mancusoa74/Walvola/Software/Walvola/telegram.cpp

//#include "telegram.h"

//TelegramBOT tgram_bot(TGRAM_BOTtoken, TGRAM_BOTname, TGRAM_BOTusername);
//String tgram_listener[TGRAM_LISTENER_SIZE] =  { "YOUR TELEGRAM BOT CHAT ID" };

//void tgram_sendmex(String message)
//{
//        TelegramBOT tgram_bot(TGRAM_BOTtoken, TGRAM_BOTname, TGRAM_BOTusername);
//        String tgram_listener[TGRAM_LISTENER_SIZE] =  { "YOUR TELEGRAM BOT CHAT ID" };
//
//        tgram_bot.begin();    
//        for (int i = 0; i < TGRAM_LISTENER_SIZE; i++) 
//        {
//               log("Sending telegram message to...");
//                log(tgram_listener[i]);
//                log("Telegram message:: " + message);
//                //tgram_bot.sendMessage(tgram_listener[i], message, "");    
//        }
//}
