mancusoa74/Walvola/Software/Walvola/telegram.h

//#ifndef TELEGRAM_H
//#define TELEGRAM_H
//
//#include "Walvola.h"
//
//#define TGRAM_BOTtoken       "YOUR TELEGRAM BOT TOKEN" //your telegram BOT token
//#define TGRAM_BOTname        "YOUR TELEGRAM BOT NAME"                                          //your telegram BOT name
//#define TGRAM_BOTusername    "YOUR TELEFRAM BOT USER NAME"                                      //your telegram BOT username
//#define TGRAM_LISTENER_SIZE  1                                               
//
////forward declaration
//void tgram_sendmex(String message);
//
//#endif
