mancusoa74/Walvola/Software/Walvola/keen.h

#ifndef KEEN_H
#define KEEN_H

#include "Walvola.h"

#define KEEN_PROJECT_ID  "YOUR KEEN.IO PROJECT ID" //your unique keen.io project id
#define KEEN_MASTER_KEY  "YOUR KEEN.IO MASTER KEY" //your unique keen.io master key

//forward declaration
void keen_post(String collection, String data);

#endif
