mancusoa74/Walvola/Software/Walvola/json.h

#ifndef JSON_H
#define JSON_H

#include "Walvola.h"

#define KV_SIZE            16//32
#define JSON_KVS           8//16
#define JSON_MEX_MAX_SIZE  128//256

//forward declaration
int mqtt2JSONkvs(String mex);
String getJSONvalue(char * key);

#endif
